Kimishiba/Tiny-AI-Limits/docs/assets/concepts/concept_a_telemetry_ping.gif

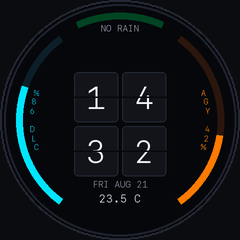
docs/assets/concepts/concept_a_telemetry_ping.gif
