Kimishiba/Tiny-AI-Limits/docs/assets/round/26846-TFT-round-1.28-1.webp

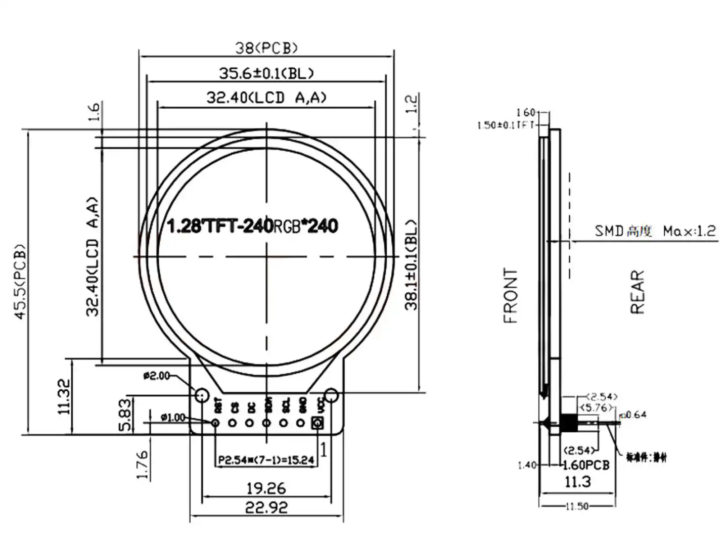
docs/assets/round/26846-TFT-round-1.28-1.webp
