Kimishiba/Tiny-AI-Limits/docs/assets/round/mascot_frames/frame_000.png

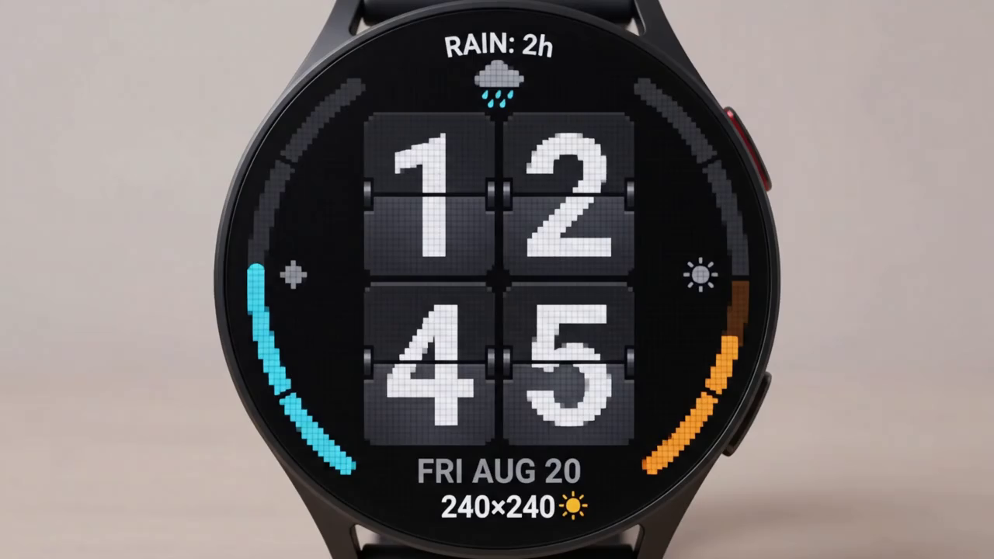
docs/assets/round/mascot_frames/frame_000.png
