Kimishiba/Tiny-AI-Limits/docs/assets/round/mascot_frames/frame_25pct.png

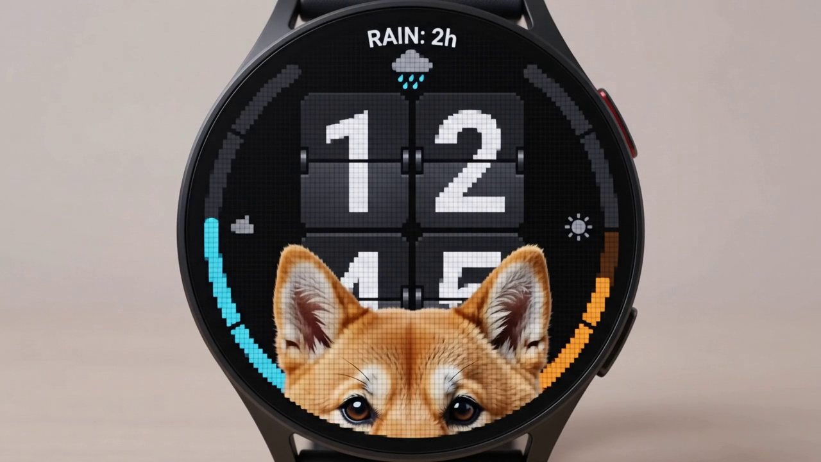
docs/assets/round/mascot_frames/frame_25pct.png
