Kimishiba/Tiny-AI-Limits/docs/assets/round/mascot_frames/frame_50pct.png

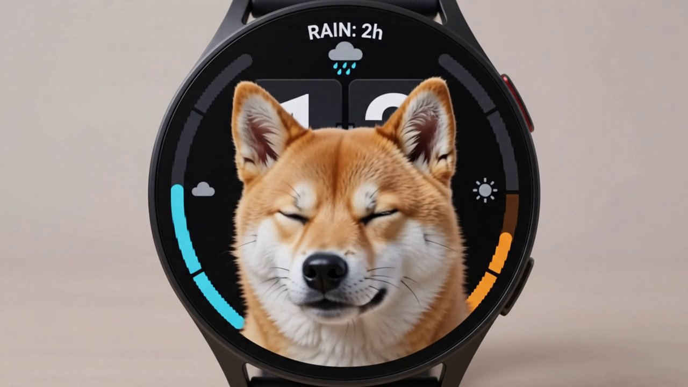
docs/assets/round/mascot_frames/frame_50pct.png
