Kimishiba/Tiny-AI-Limits/docs/assets/round/mascot_frames/frame_75pct.png

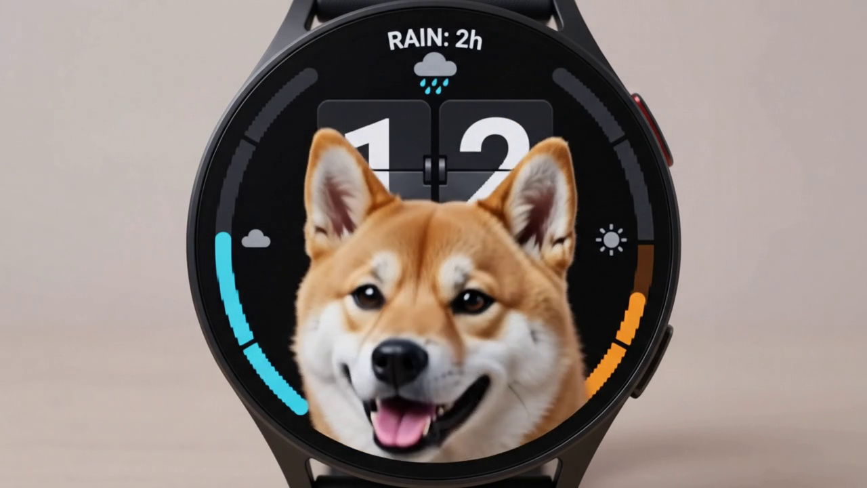
docs/assets/round/mascot_frames/frame_75pct.png
