Kimishiba/Tiny-AI-Limits/docs/assets/round/mascot_frames/screen_f0_240.png

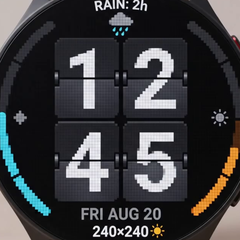
docs/assets/round/mascot_frames/screen_f0_240.png
