Kimishiba/Tiny-AI-Limits/docs/assets/round/mascot_frames/screen_fdog_240.png

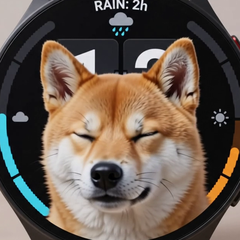
docs/assets/round/mascot_frames/screen_fdog_240.png
