Kimishiba/Tiny-AI-Limits/docs/assets/round/stand_crop_front.png

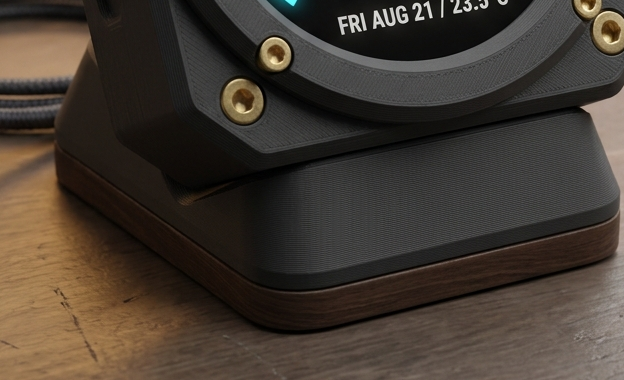
docs/assets/round/stand_crop_front.png
