Kimishiba/Tiny-AI-Limits/docs/assets/round/stand_crop_rear.png

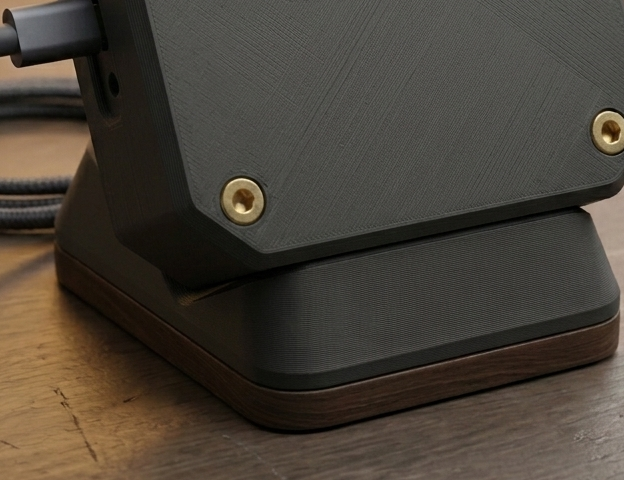
docs/assets/round/stand_crop_rear.png
