Kimishiba/Tiny-AI-Limits/docs/assets/round/stand_cross_section_true_upright.png

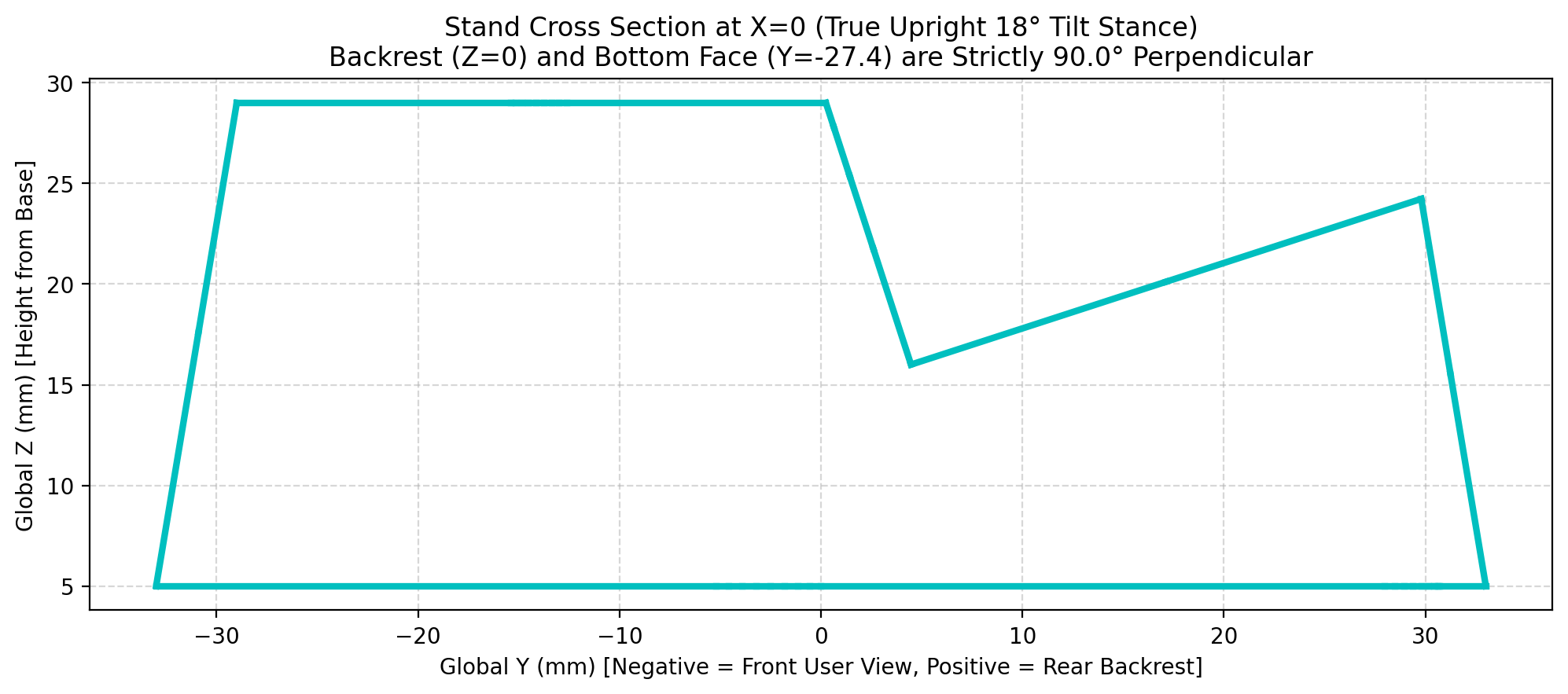
docs/assets/round/stand_cross_section_true_upright.png
