Kimishiba/Tiny-AI-Limits/round 240x240/enclosure/esp32c3_supermini_dimensions.png

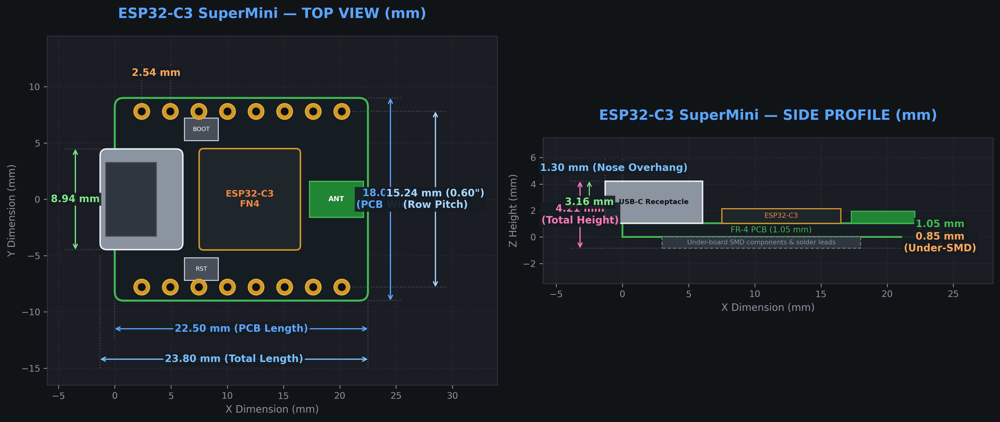
round 240x240/enclosure/esp32c3_supermini_dimensions.png
