Kimishiba/Tiny-AI-Limits/round 240x240/enclosure/usbc_option2_vs_option3.png

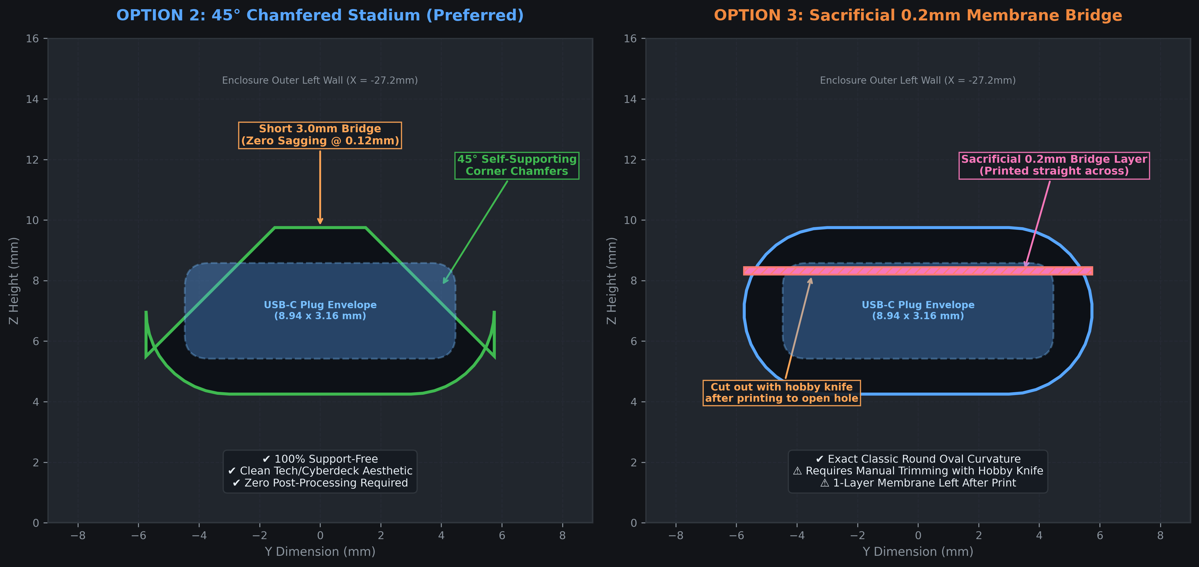
round 240x240/enclosure/usbc_option2_vs_option3.png
