Kimishiba/Tiny-AI-Limits/round 360x360/enclosure/screen_cad_detail.png

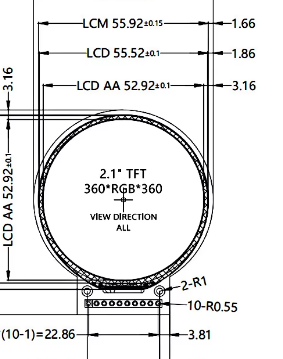
round 360x360/enclosure/screen_cad_detail.png
