Kimishiba/Tiny-AI-Limits/square 240x240/assets/square_enclosure_3d_render.jpg

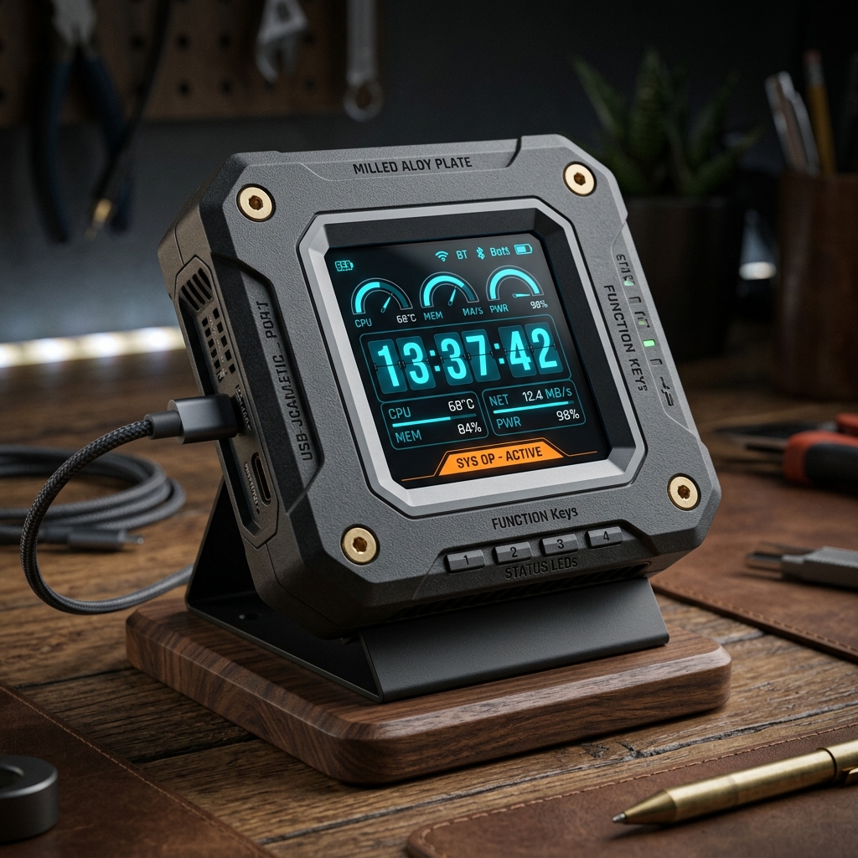
square 240x240/assets/square_enclosure_3d_render.jpg
