Kimishiba/Tiny-AI-Limits/round 240x240/enclosure/gc9a01_minimalist_stand.stl

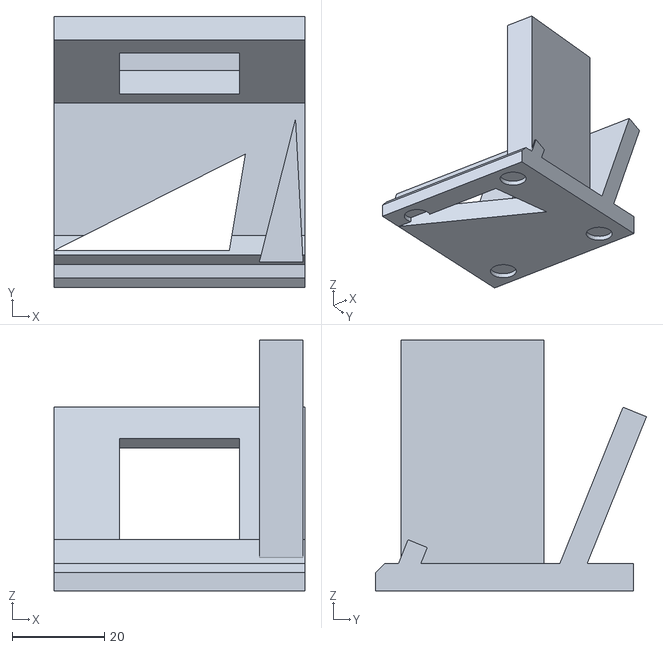
[picture p44: CAD file, 2026-08-31]
round 240x240/enclosure/gc9a01_minimalist_stand.stl
54.4 x 58.8 x 54.4
