Kimishiba/Tiny-AI-Limits/round 240x240/enclosure/gc9a01_u_bracket_kickstand.stl

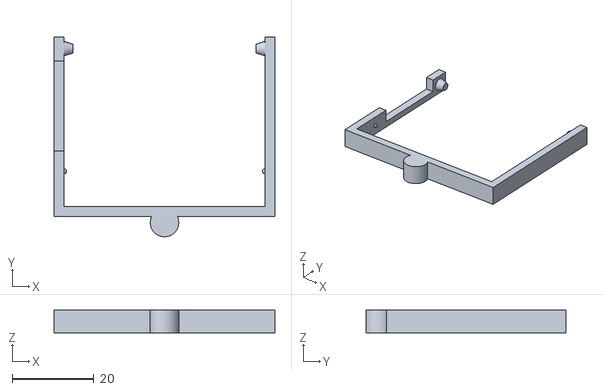
[picture p45: CAD file, 2026-08-28]
round 240x240/enclosure/gc9a01_u_bracket_kickstand.stl
54.0 x 48.8 x 5.60
