Kimishiba/Tiny-AI-Limits/round 240x240/enclosure/esp32_s3_supermini_carrier.stl

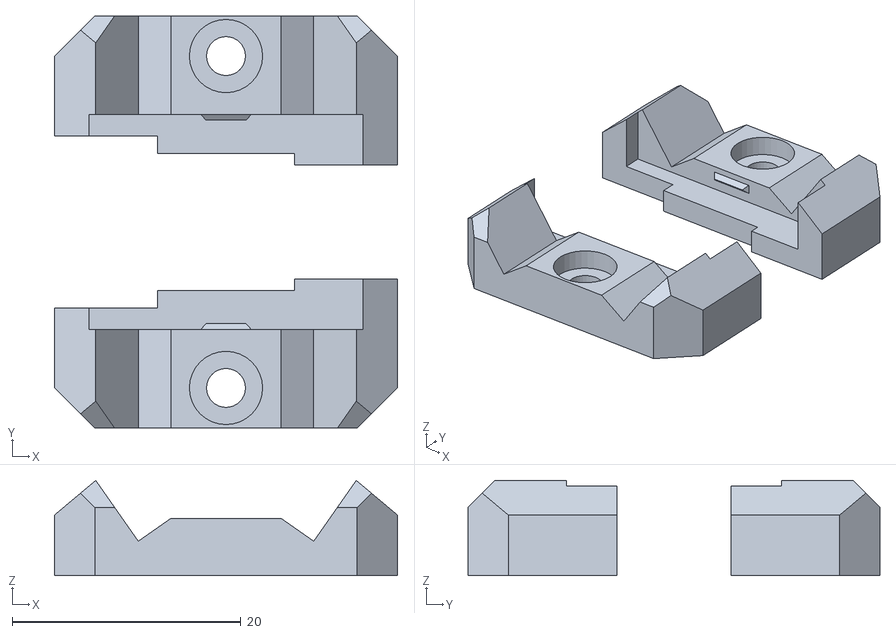
[picture p46: CAD file, 2026-08-28]
round 240x240/enclosure/esp32_s3_supermini_carrier.stl
30.0 x 36.0 x 8.31
