Kimishiba/Tiny-AI-Limits/round 240x240/enclosure/gc9a01_stand_tier1_base.stl

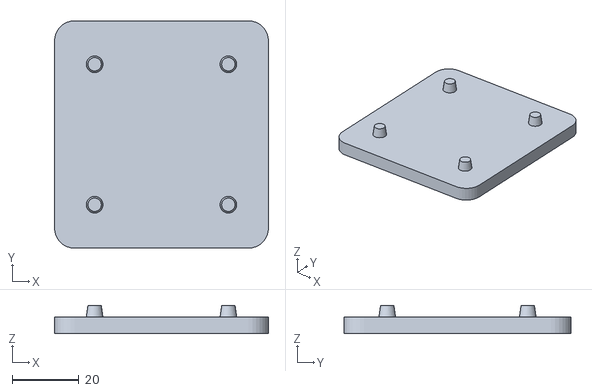
[picture p47: CAD file, 2026-08-24]
round 240x240/enclosure/gc9a01_stand_tier1_base.stl
64.0 x 68.0 x 8.50
