Kimishiba/Tiny-AI-Limits/round 240x240/enclosure/gc9a01_stand_accent_base.stl

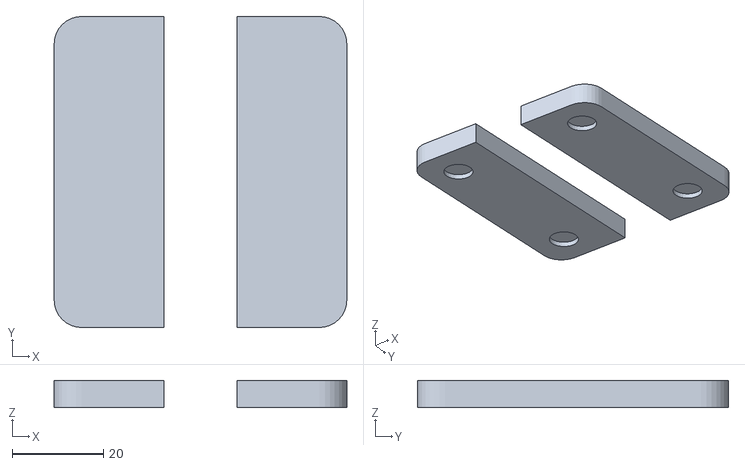
[picture p48: CAD file, 2026-08-24]
round 240x240/enclosure/gc9a01_stand_accent_base.stl
64.0 x 68.0 x 6.00
