Kimishiba/Tiny-AI-Limits/docs/assets/round/stand_verification_render.png

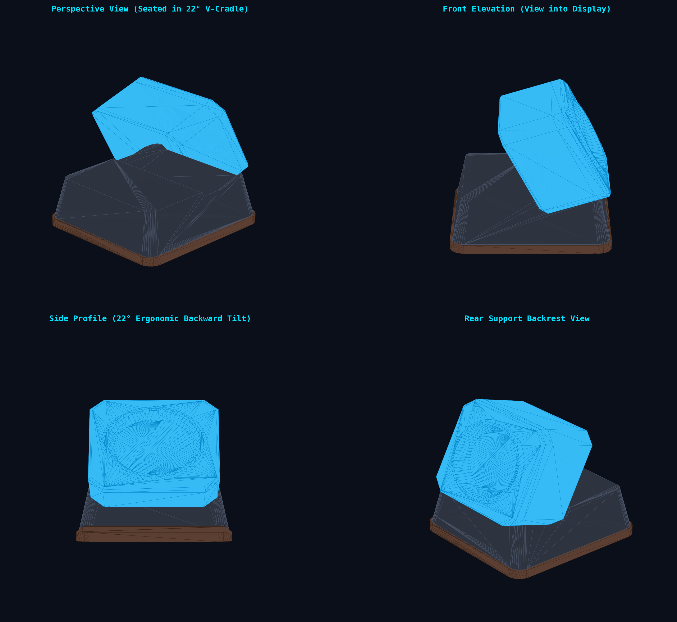
docs/assets/round/stand_verification_render.png
